atb4c/monster_m4sk_candy_bowl/assets/bowl_assembly.png

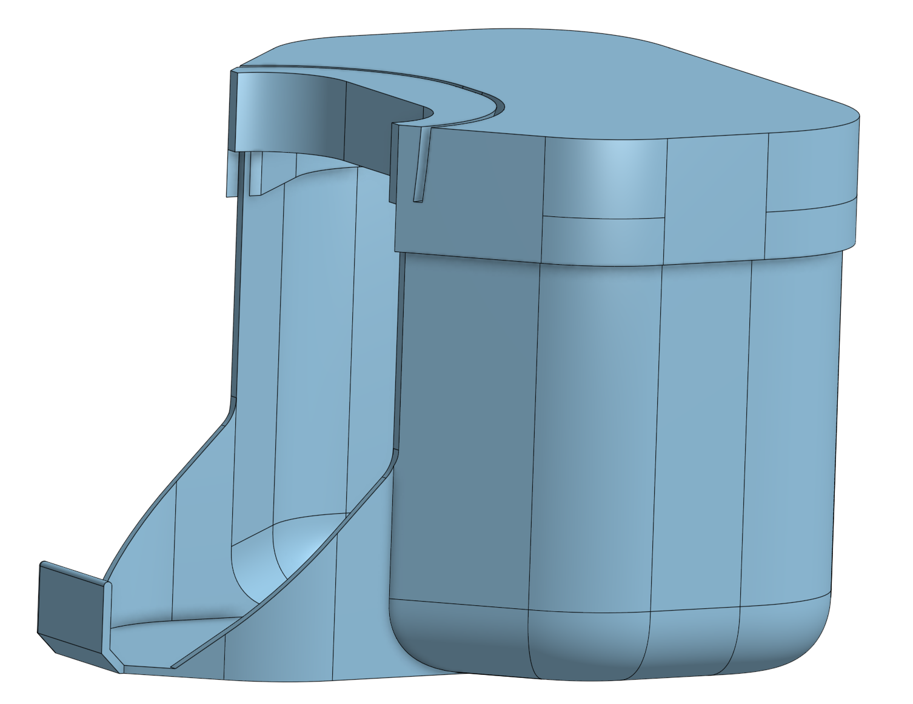
assets/bowl_assembly.png
